miata-bot/can-link/hardware/underglow-controller/images/v5/tc2030-idc.png

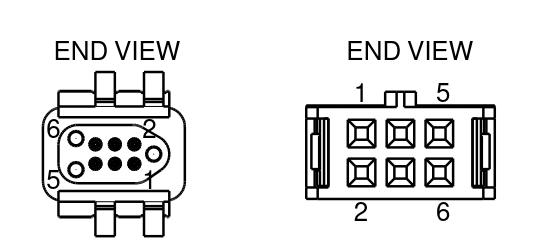
hardware/underglow-controller/images/v5/tc2030-idc.png
