miata-bot/can-link/hardware/underglow-controller/images/v5/tc2050-idc.png

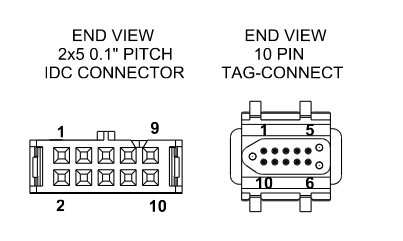
hardware/underglow-controller/images/v5/tc2050-idc.png
