miata-bot/can-link/hardware/underglow-controller/images/prototype/prototype-wiring.jpg

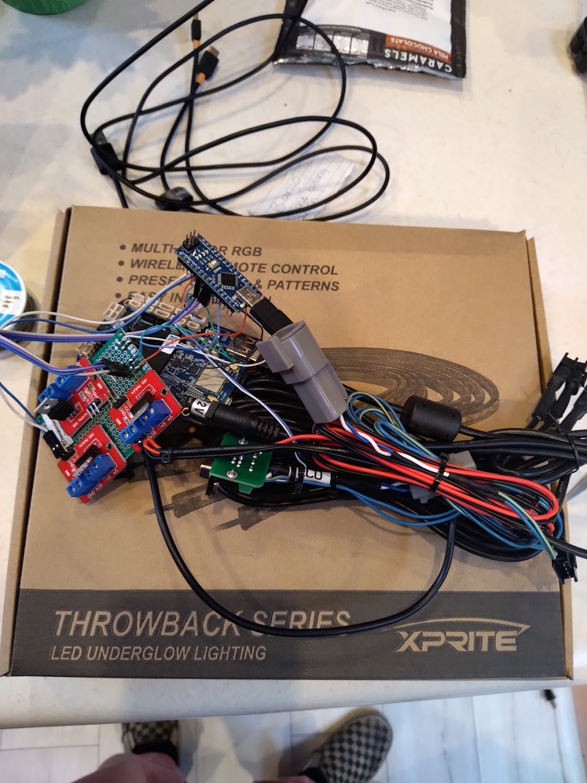
hardware/underglow-controller/images/prototype/prototype-wiring.jpg
