miata-bot/can-link/hardware/underglow-controller/images/wiring/CAN-DTM-Connector-Male.jpg

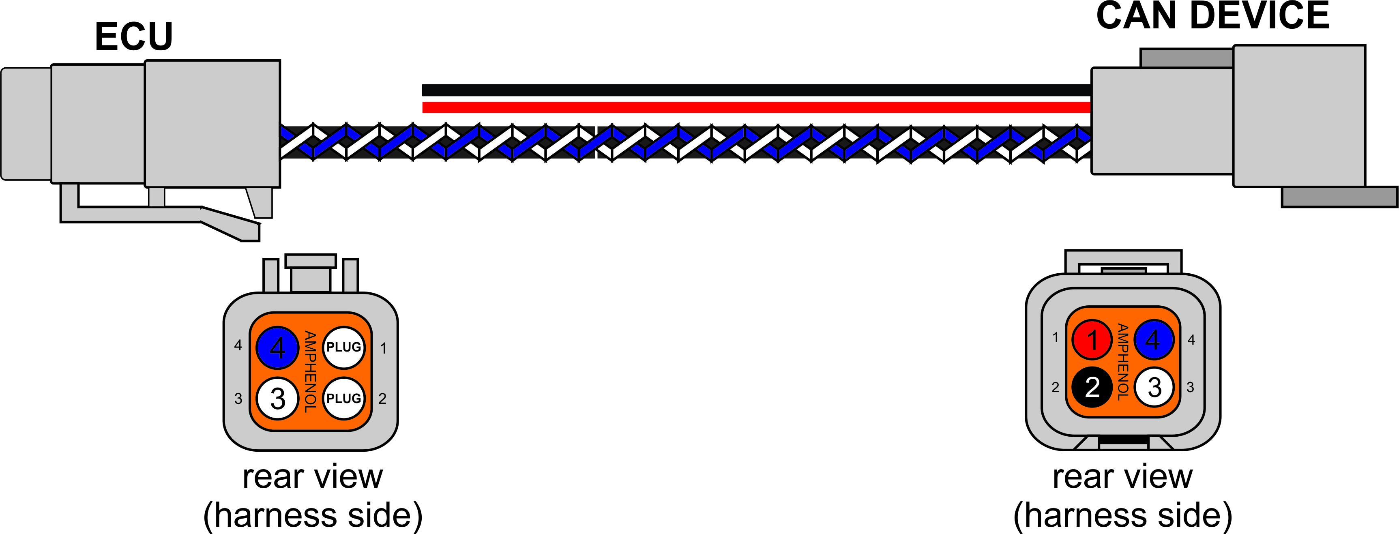
hardware/underglow-controller/images/wiring/CAN-DTM-Connector-Male.jpg
