miata-bot/can-link/hardware/underglow-controller/images/wiring/JST-SM-Female.png

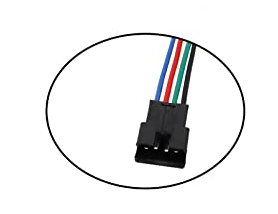
hardware/underglow-controller/images/wiring/JST-SM-Female.png
