miata-bot/can-link/hardware/underglow-controller/images/wiring/JST-SM-Male.png

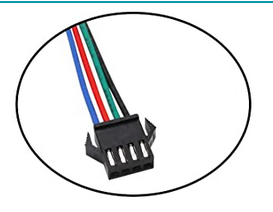
hardware/underglow-controller/images/wiring/JST-SM-Male.png
