miata-bot/can-link/hardware/underglow-controller/images/wiring/OutputRegulator-Calculations.png

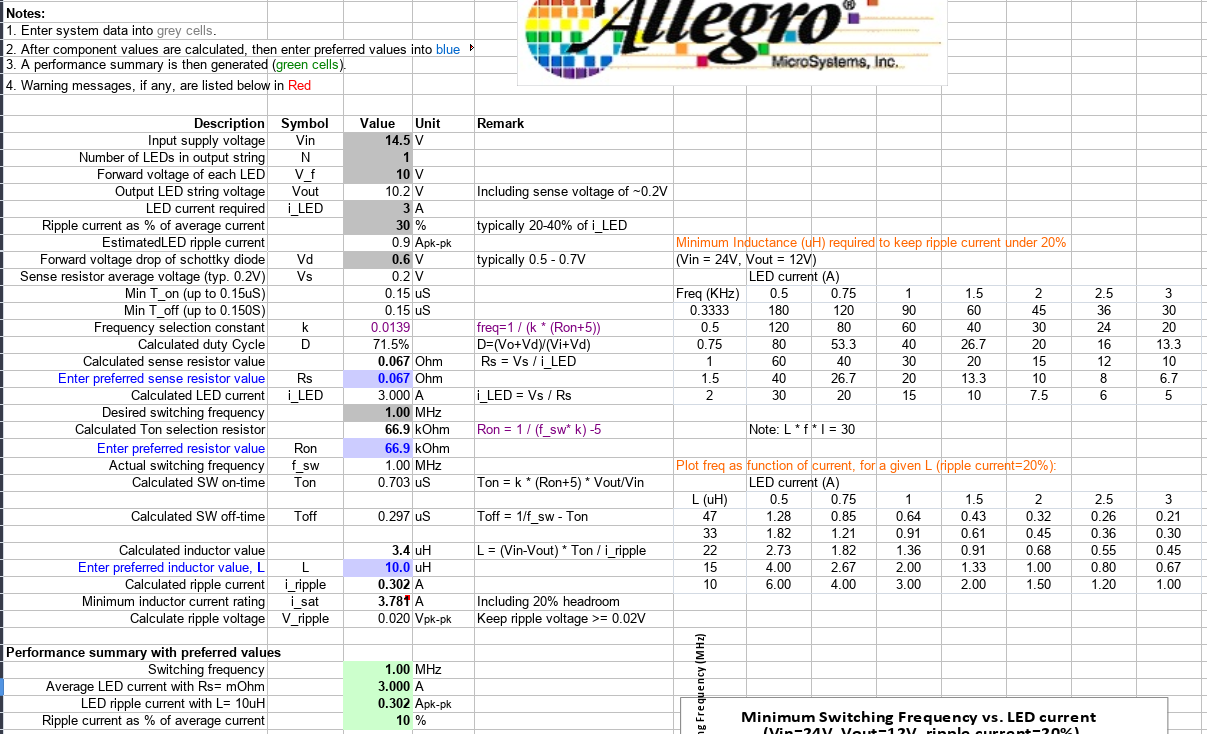
hardware/underglow-controller/images/wiring/OutputRegulator-Calculations.png
