miata-bot/can-link/hardware/underglow-controller/images/wiring/Plug-Female.png

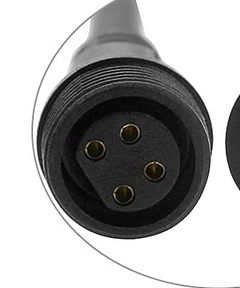
hardware/underglow-controller/images/wiring/Plug-Female.png
