miata-bot/can-link/hardware/underglow-controller/images/wiring/Plug-Male.png

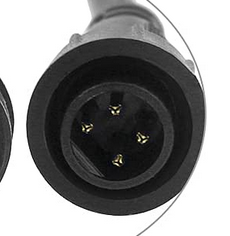
hardware/underglow-controller/images/wiring/Plug-Male.png
