miata-bot/can-link/hardware/underglow-controller/images/wiring/Relay-Socket.png

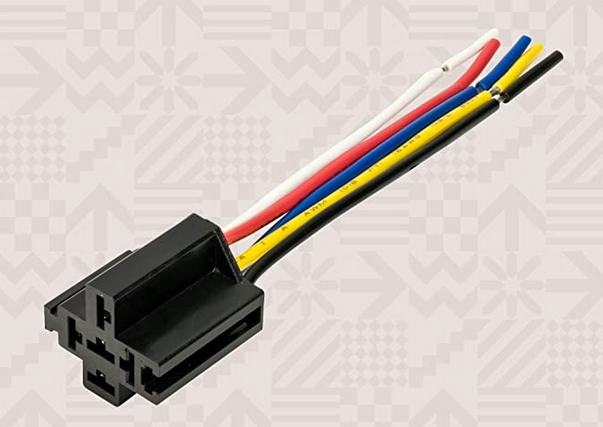
hardware/underglow-controller/images/wiring/Relay-Socket.png
