miata-bot/can-link/hardware/underglow-controller/images/wiring/RGB-Extension.png

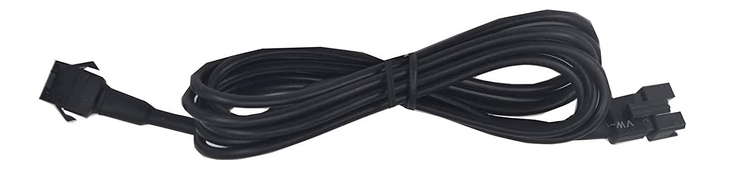
hardware/underglow-controller/images/wiring/RGB-Extension.png
