miata-bot/can-link/hardware/underglow-controller/images/wiring/RGB-Male.png

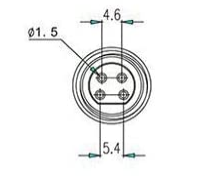
hardware/underglow-controller/images/wiring/RGB-Male.png
