miata-bot/can-link/hardware/underglow-controller/images/wiring/USB-Connector-Female.png

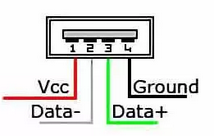
hardware/underglow-controller/images/wiring/USB-Connector-Female.png
